patricktlo/IotSoilSensor/1_Simulations/Moisture sensor/Simulation/FEMM Files/Images/w05d03.png

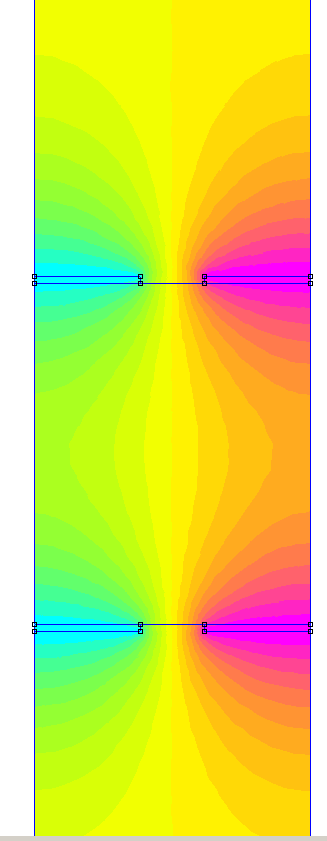
1_Simulations/Moisture sensor/Simulation/FEMM Files/Images/w05d03.png
