patricktlo/IotSoilSensor/1_Simulations/Moisture sensor/Images/sq_withsensor.png

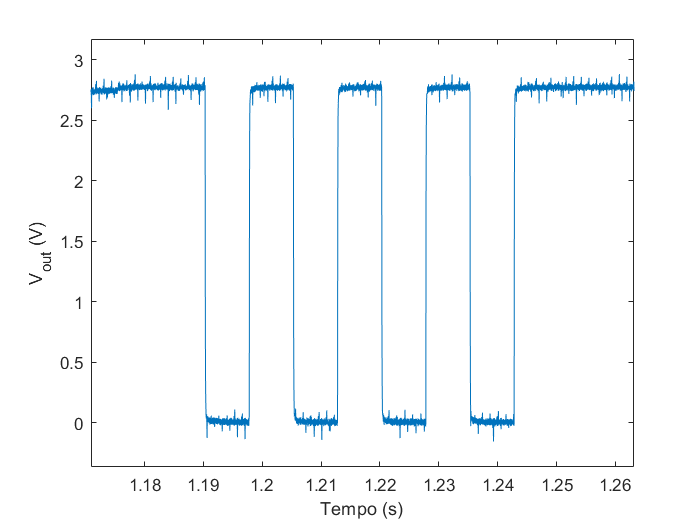
1_Simulations/Moisture sensor/Images/sq_withsensor.png
