patricktlo/IotSoilSensor/1_Simulations/Moisture sensor/Simulation/FEMM Files/Images/w05_d03_air.png

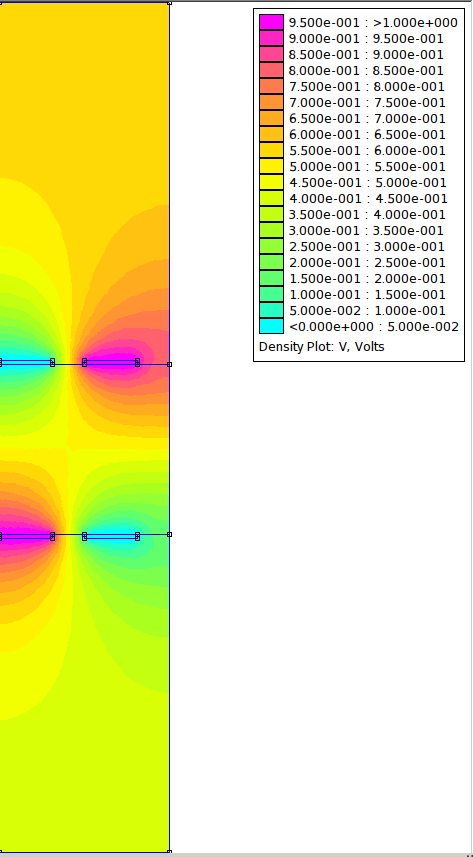
1_Simulations/Moisture sensor/Simulation/FEMM Files/Images/w05_d03_air.png
