patricktlo/IotSoilSensor/1_Simulations/Moisture sensor/Simulation/FEMM Files/Images/w05_d05_air.png

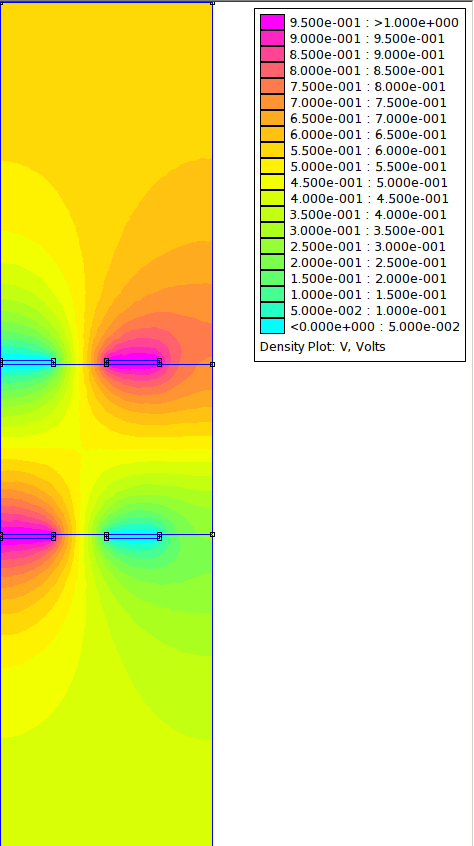
1_Simulations/Moisture sensor/Simulation/FEMM Files/Images/w05_d05_air.png
