patricktlo/IotSoilSensor/1_Simulations/HR202/hr202.asc

C1: cap; 4.7n
C2: cap; 1n
R1: res; {R}
R2: res; 47k
R3: res; 47k
V1: voltage; 3
V2: voltage; PULSE(0 3 0 1n 1n 128m 256m 10)
Named nets: 0, Vout, Vcc
.tran 1
.step param R list 3k 13k 87k 1.3meg
Comment this in case you just want to test one value
HR202 model
