patricktlo/IotSoilSensor/1_Simulations/Moisture sensor/Simulation/LTSpice/MS.asc

C1: cap; {C}
R1: res; 240k
R2: res; 22k
R3: res; 22K
V1: voltage; 1
V2: voltage; PULSE(0 1 0 1n 1n 7.5m 15m 100)
Named nets: 0, Vcc
.tran 0 20m 0
.step param C 50p 2n 500p
Comment below if you only want one value
