patricktlo/IotSoilSensor/3_Software/Device/IotSoilSensor/Inc/GPIO.h

#include "main.h"

// NTC functions
void GPIO_NTC_on();
void GPIO_NTC_off();

// HR202 functions
void HR202_init();
void GPIO_HR202_on();
void GPIO_HR202_off();
void GPIO_HR202_timer_off();

// MS functions
void GPIO_MS_on();
void GPIO_MS_off();
void GPIO_MS_timer_off();

// User led
void GPIO_userLed_on();
void GPIO_userLed_off();
