patricktlo/IotSoilSensor/3_Software/Device/IotSoilSensor/Inc/COMP.h

/*
 * COMP.h
 *
 *  Created on: 5 de nov de 2018
 *      Author: patrick
 */

#ifndef COMP_H_
#define COMP_H_

#include "main.h"

void COMP_start();

void COMP_stop();

void COMP_init();

uint32_t COMP_getOutput();

#endif /* COMP_H_ */
