patricktlo/IotSoilSensor/3_Software/Device/IotSoilSensor/Inc/timer.h

#include "main.h"

// HR202
void timer_HR202_init();

void timer_HR202_start_square();

void timer_HR202_stop_square();

void timer_HR202_reset();

bool timer_HR202_checkToggle();

uint16_t timer_HR202_getTimer();

// Moisture sensor
void timer_MS_init();

void timer_MS_start_square();

void timer_MS_stop_square();

bool timer_MS_checkToggle();

void timer_MS_reset();

uint16_t timer_MS_getTimer();
