patricktlo/IotSoilSensor/3_Software/Device/IotSoilSensor/test/test_MoistureSensor.c

#include "unity.h"
#include "MoistureSensor.h"

void setUp(void)
{
}

void tearDown(void)
{
}

void test_MoistureSensor_NeedToImplement(void)
{
    TEST_IGNORE_MESSAGE("Need to Implement MoistureSensor");
}
